fabsss/lambda_monitor/src/ota_task.c

#include "ota_task.h"
#include "esp_ota_ops.h"
#include "esp_log.h"
#include "freertos/FreeRTOS.h"
#include "freertos/task.h"

static const char *TAG = "ota_task";
#define OTA_RECV_BUF_SIZE 1024

void ota_task_mark_valid_if_pending(void)
{
    const esp_partition_t *running = esp_ota_get_running_partition();
    esp_ota_img_states_t state;

    if (esp_ota_get_state_partition(running, &state) == ESP_OK) {
        if (state == ESP_OTA_IMG_PENDING_VERIFY) {
            esp_ota_mark_app_valid_cancel_rollback();
            ESP_LOGI(TAG, "OTA image marked valid");
        }
    }
}

/* Intentionally unauthenticated: this device runs its own SoftAP with no
 * internet uplink, so /api/ota is only reachable by a client already
 * associated to the AP (accepted risk for this single-user hobby device). */
esp_err_t ota_task_handle_upload(httpd_req_t *req)
{
    const esp_partition_t *update_partition = esp_ota_get_next_update_partition(NULL);
    if (!update_partition) {
        httpd_resp_send_err(req, HTTPD_500_INTERNAL_SERVER_ERROR, "No OTA partition");
        return ESP_FAIL;
    }

    if (req->content_len <= 0 || (size_t)req->content_len > update_partition->size) {
        ESP_LOGE(TAG, "OTA upload rejected: content_len=%d partition_size=%lu",
                 req->content_len, update_partition->size);
        httpd_resp_send_err(req, HTTPD_400_BAD_REQUEST, "Invalid or oversized image");
        return ESP_FAIL;
    }

    esp_ota_handle_t ota_handle;
    esp_err_t err = esp_ota_begin(update_partition, req->content_len, &ota_handle);
    if (err != ESP_OK) {
        ESP_LOGE(TAG, "esp_ota_begin failed: %s", esp_err_to_name(err));
        httpd_resp_send_err(req, HTTPD_500_INTERNAL_SERVER_ERROR, "OTA begin failed");
        return ESP_FAIL;
    }

    char buf[OTA_RECV_BUF_SIZE];
    int remaining = req->content_len;

    while (remaining > 0) {
        int to_read = remaining < (int)sizeof(buf) ? remaining : (int)sizeof(buf);
        int received = httpd_req_recv(req, buf, to_read);
        if (received == HTTPD_SOCK_ERR_TIMEOUT) {
            continue;
        }
        if (received <= 0) {
            ESP_LOGE(TAG, "OTA recv failed: %d", received);
            esp_ota_abort(ota_handle);
            httpd_resp_send_err(req, HTTPD_500_INTERNAL_SERVER_ERROR, "Upload interrupted");
            return ESP_FAIL;
        }

        err = esp_ota_write(ota_handle, buf, received);
        if (err != ESP_OK) {
            ESP_LOGE(TAG, "esp_ota_write failed: %s", esp_err_to_name(err));
            esp_ota_abort(ota_handle);
            httpd_resp_send_err(req, HTTPD_500_INTERNAL_SERVER_ERROR, "Flash write failed");
            return ESP_FAIL;
        }
        remaining -= received;
    }

    err = esp_ota_end(ota_handle);
    if (err != ESP_OK) {
        ESP_LOGE(TAG, "esp_ota_end failed (invalid image?): %s", esp_err_to_name(err));
        httpd_resp_send_err(req, HTTPD_400_BAD_REQUEST, "Image validation failed");
        return ESP_FAIL;
    }

    err = esp_ota_set_boot_partition(update_partition);
    if (err != ESP_OK) {
        ESP_LOGE(TAG, "esp_ota_set_boot_partition failed: %s", esp_err_to_name(err));
        httpd_resp_send_err(req, HTTPD_500_INTERNAL_SERVER_ERROR, "Boot partition set failed");
        return ESP_FAIL;
    }

    httpd_resp_set_type(req, "application/json");
    httpd_resp_send(req, "{\"ok\":true,\"rebooting\":true}", HTTPD_RESP_USE_STRLEN);
    vTaskDelay(pdMS_TO_TICKS(500));
    esp_restart();
    return ESP_OK;
}
